paenian/beltalowda/dxfs/ab2_spacer_plates.dxf

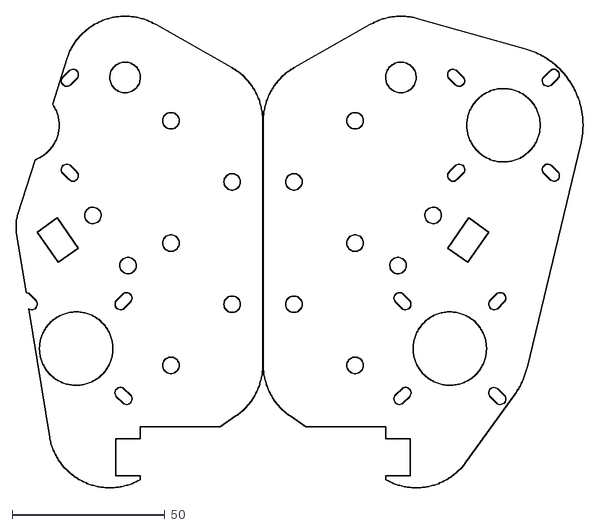
[picture p15: CAD file, 2018-12-04]
dxfs/ab2_spacer_plates.dxf
185.4 x 154.2
