paenian/beltalowda/external_stls/Einsy-base_modified_with_door.stl

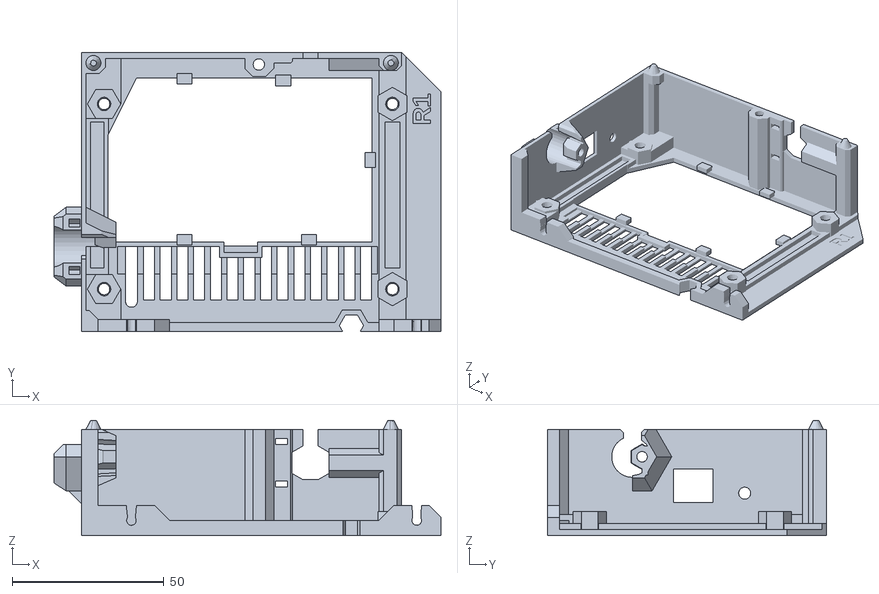
[picture p16: CAD file, 2019-01-18]
external_stls/Einsy-base_modified_with_door.stl
127.5 x 92.0 x 38.0
