paenian/beltalowda/stls/roller_drive_gear.stl

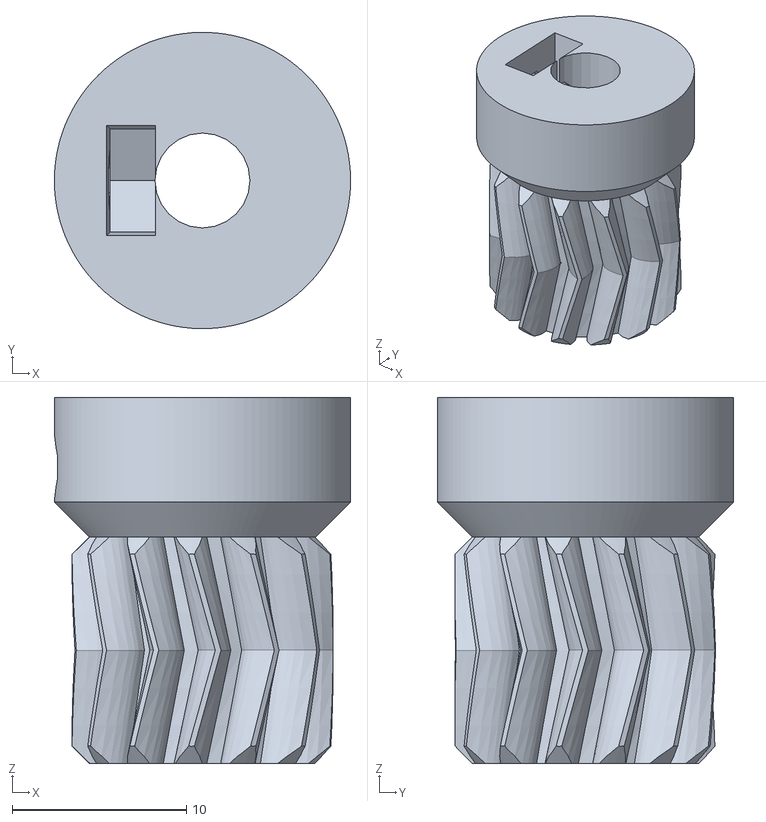
[picture p17: CAD file, 2019-01-18]
stls/roller_drive_gear.stl
17.0 x 17.0 x 21.0
