paenian/beltalowda/dxfs/corner_bracket_pair.dxf

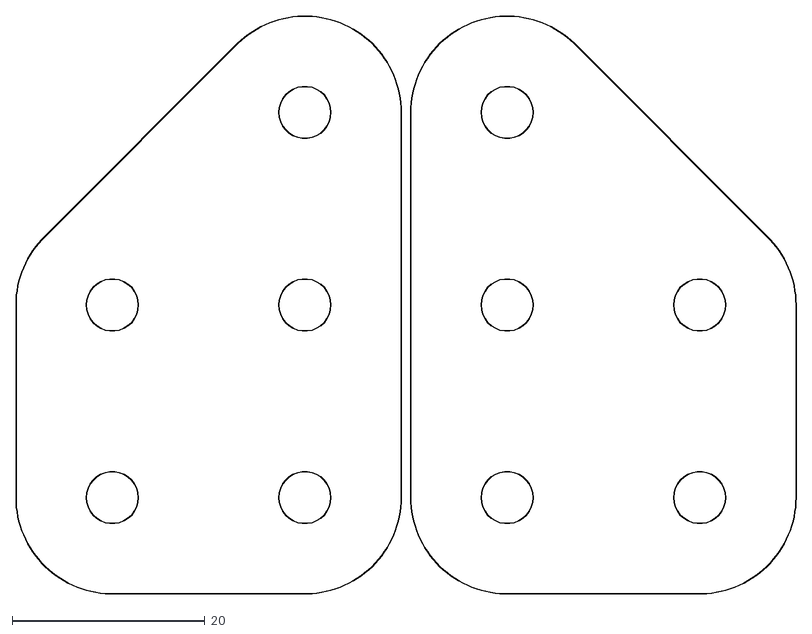
[picture p18: CAD file, 2018-11-15]
dxfs/corner_bracket_pair.dxf
81.0 x 60.0
