paenian/beltalowda/external_stls/rpi-zero-frame.stl

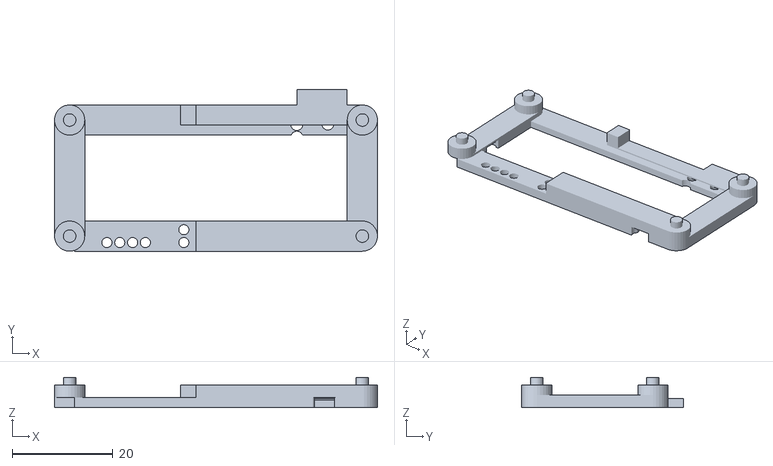
[picture p19: CAD file, 2019-01-18]
external_stls/rpi-zero-frame.stl
64.0 x 32.0 x 6.00
