paenian/beltalowda/stls/bed_front_support.stl

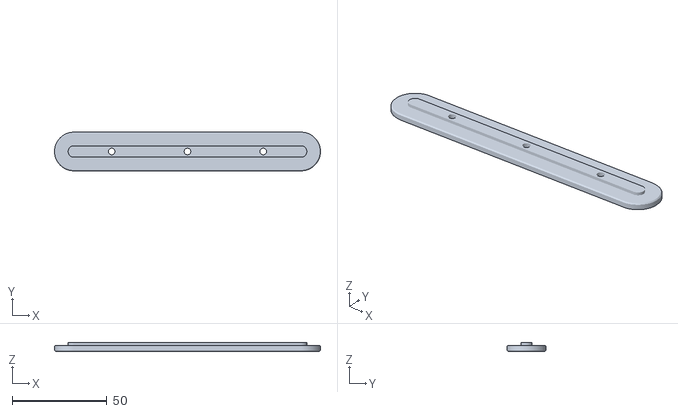
[picture p20: CAD file, 2019-01-18]
stls/bed_front_support.stl
140.4 x 20.4 x 4.58
