paenian/beltalowda/dxfs/y_front_plate.dxf

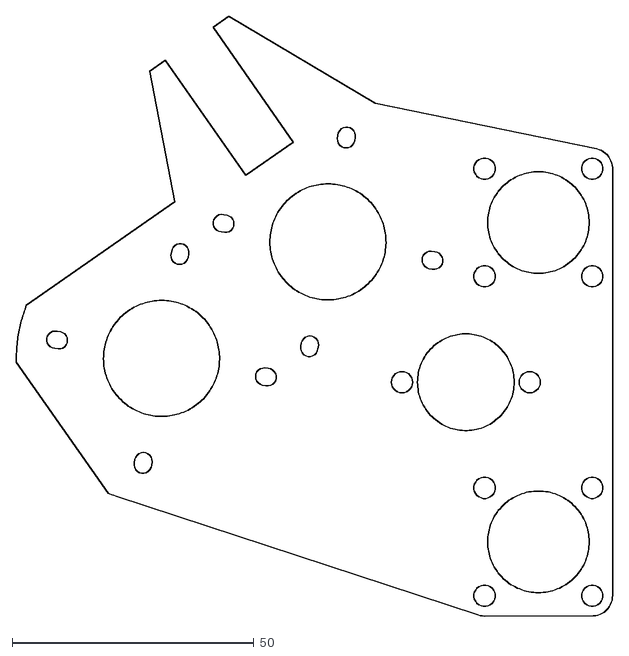
[picture p21: CAD file, 2018-11-15]
dxfs/y_front_plate.dxf
123.2 x 124.0
