paenian/beltalowda/stls/bed_side_support.stl

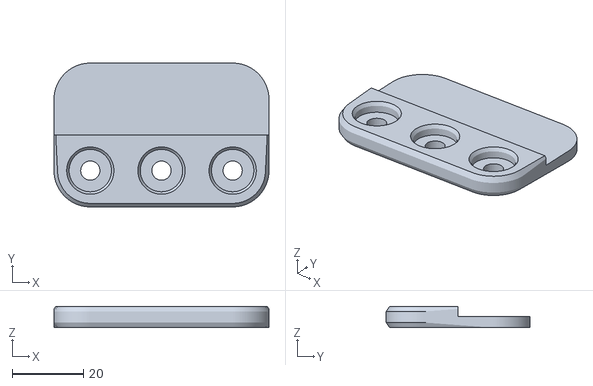
[picture p22: CAD file, 2019-01-18]
stls/bed_side_support.stl
60.4 x 40.4 x 6.00
