paenian/beltalowda/dxfs/side_plate.dxf

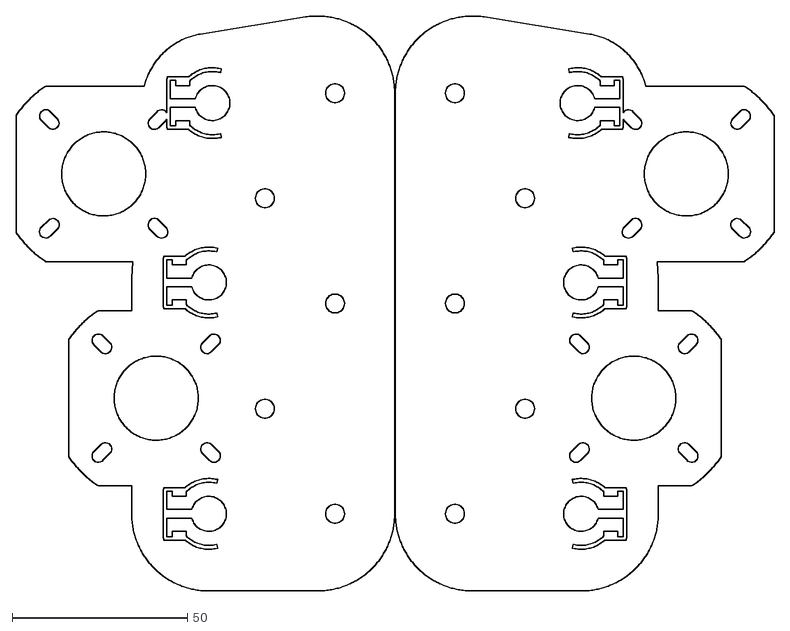
[picture p23: CAD file, 2018-11-09]
dxfs/side_plate.dxf
216.2 x 164.0
