paenian/beltalowda/stls/rubber_foot.stl

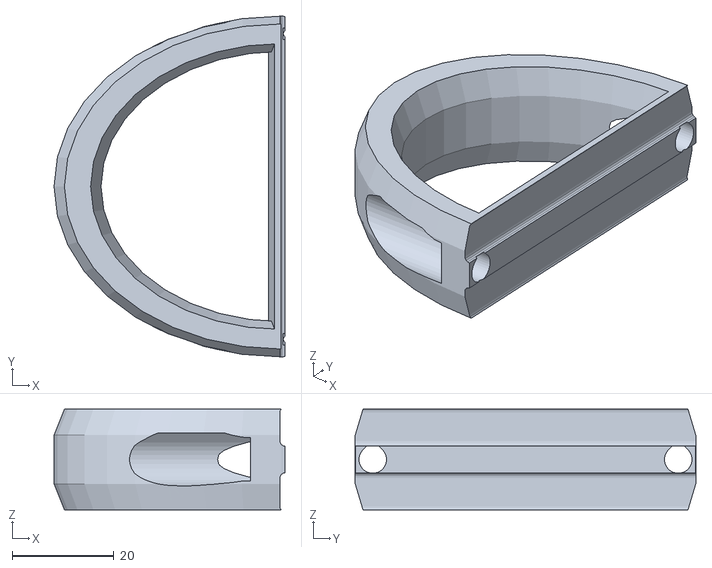
[picture p24: CAD file, 2019-01-18]
stls/rubber_foot.stl
45.4 x 66.9 x 19.8
