paenian/beltalowda/stls/roller_mount.stl

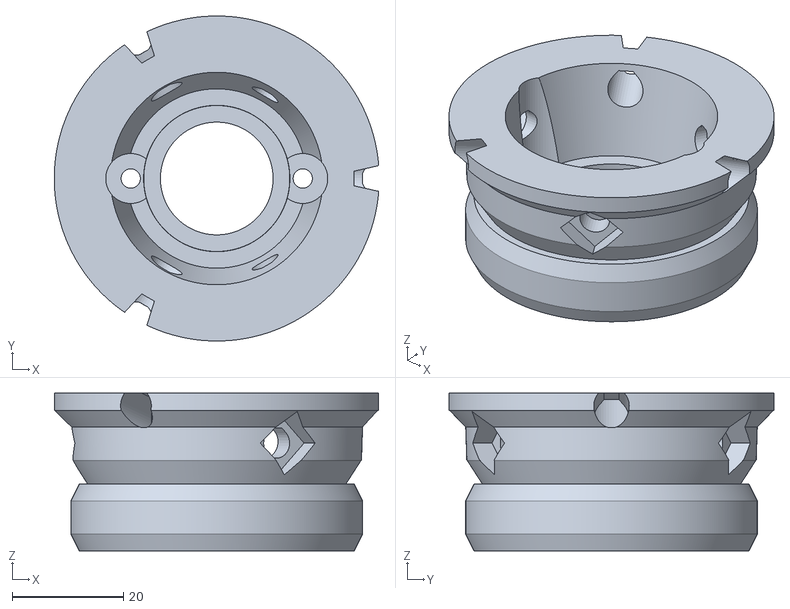
[picture p25: CAD file, 2018-12-28]
stls/roller_mount.stl
58.5 x 58.6 x 28.4
