paenian/beltalowda/stls/y_tensioner.stl

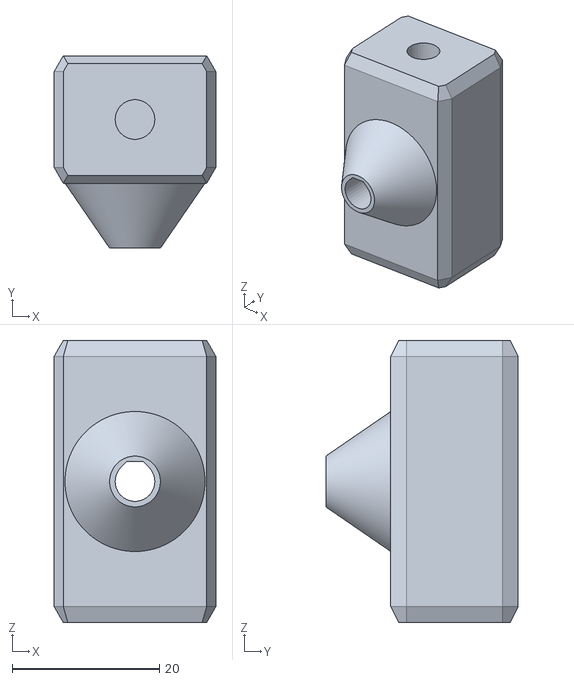
[picture p26: CAD file, 2018-12-28]
stls/y_tensioner.stl
22.0 x 26.2 x 38.3
