paenian/beltalowda/stls/y_bracket_shifted.stl

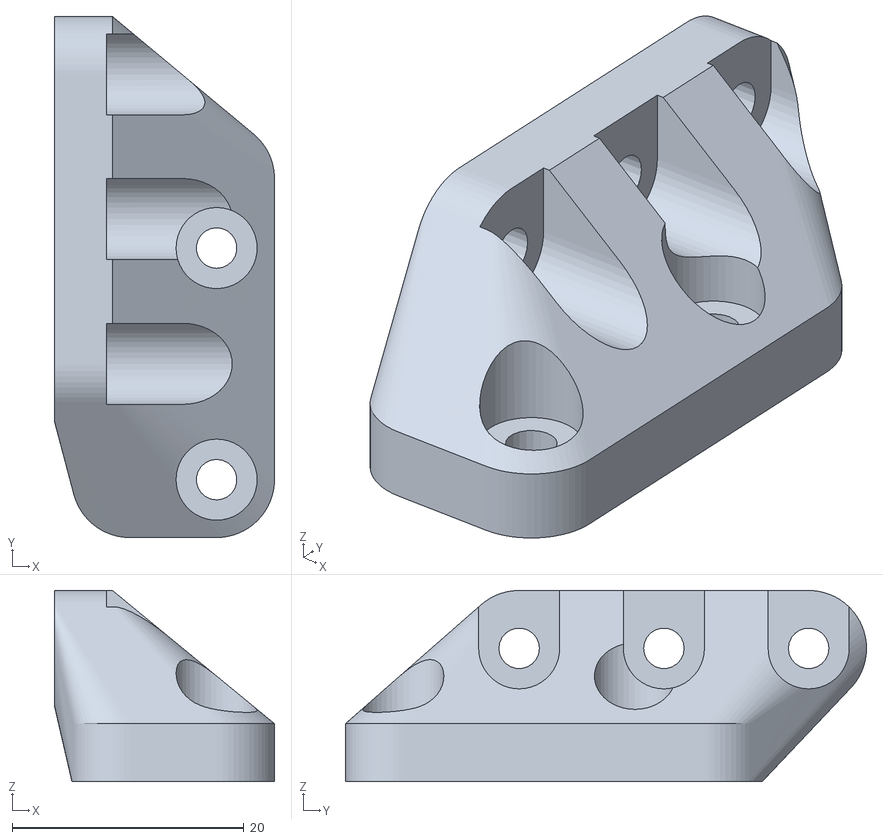
[picture p27: CAD file, 2018-12-28]
stls/y_bracket_shifted.stl
19.0 x 45.0 x 16.5
