paenian/beltalowda/stls/x_tensioner.stl

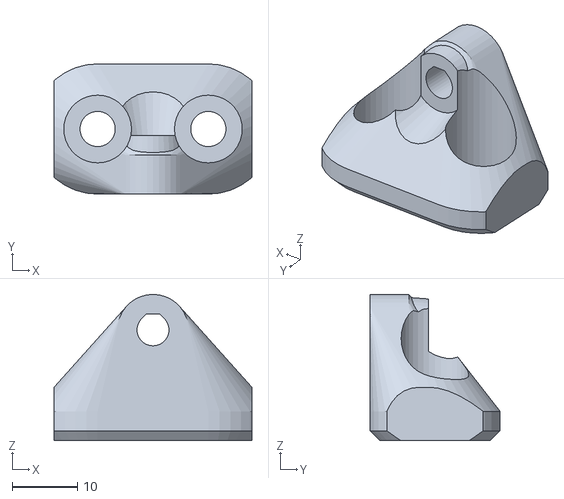
[picture p28: CAD file, 2018-12-28]
stls/x_tensioner.stl
30.4 x 20.0 x 22.4
