paenian/beltalowda/stls/x_rod_slider.stl

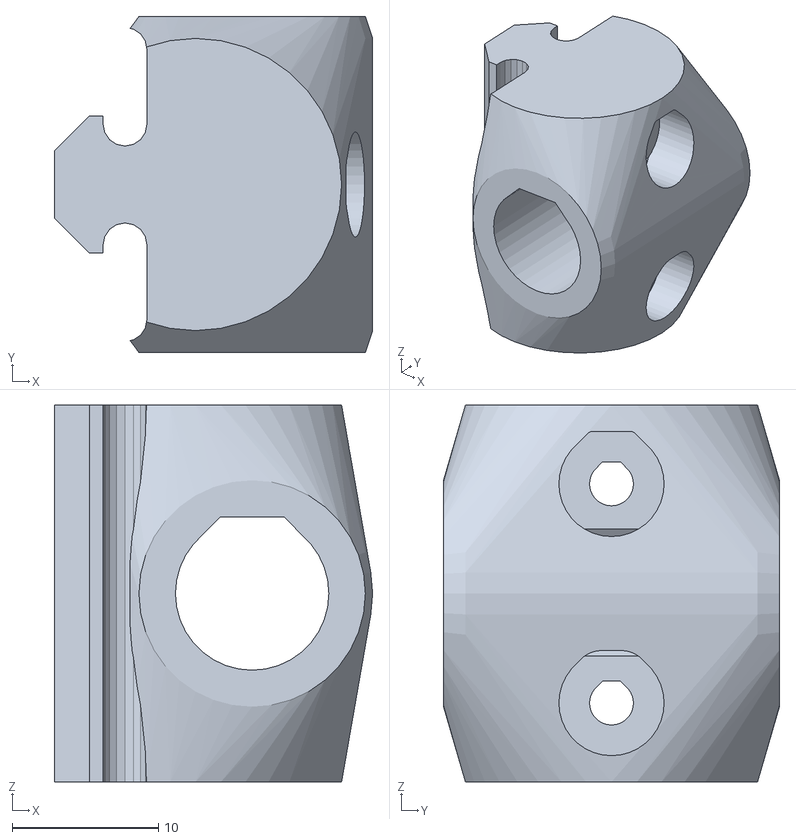
[picture p29: CAD file, 2018-12-28]
stls/x_rod_slider.stl
21.8 x 23.0 x 25.8
