paenian/beltalowda/stls/spacer.dxf

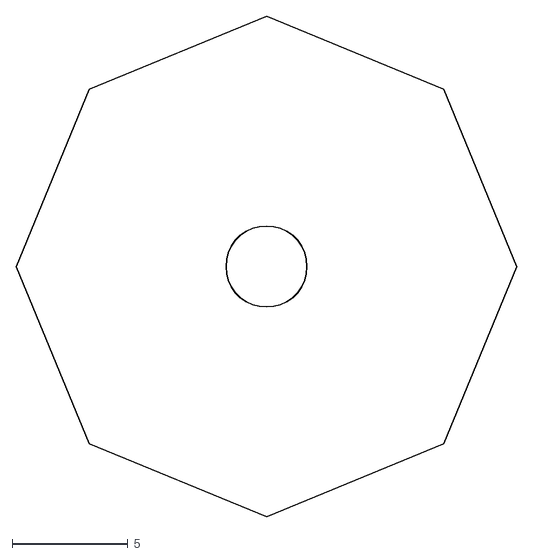
[picture p30: CAD file, 2018-12-28]
stls/spacer.dxf
21.6 x 21.6
