paenian/beltalowda/stls/y_bracket.stl

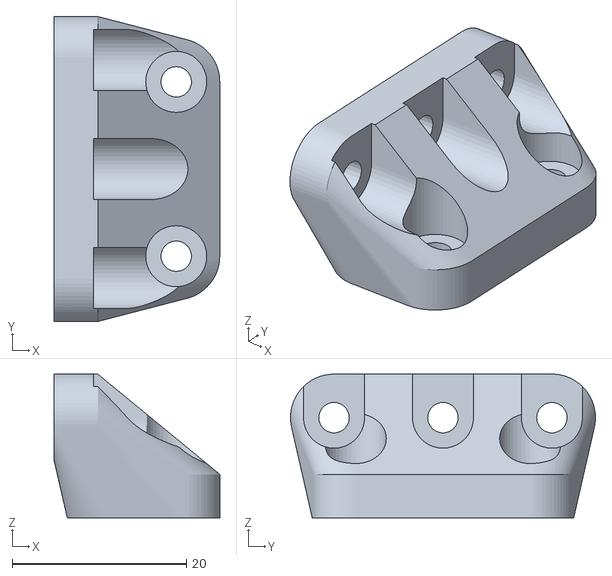
[picture p31: CAD file, 2018-12-28]
stls/y_bracket.stl
19.0 x 35.0 x 16.5
