paenian/beltalowda/stls/y_gantry.stl

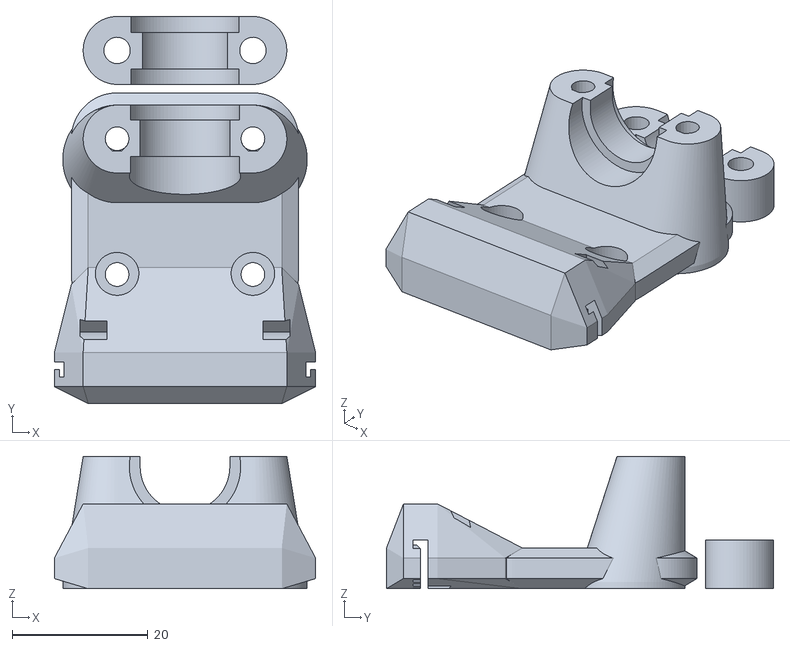
[picture p32: CAD file, 2018-12-28]
stls/y_gantry.stl
38.5 x 57.0 x 19.5
